Phyks/CitizenWatt-refactor/receiver/hardware/2017-02-15-201954.png

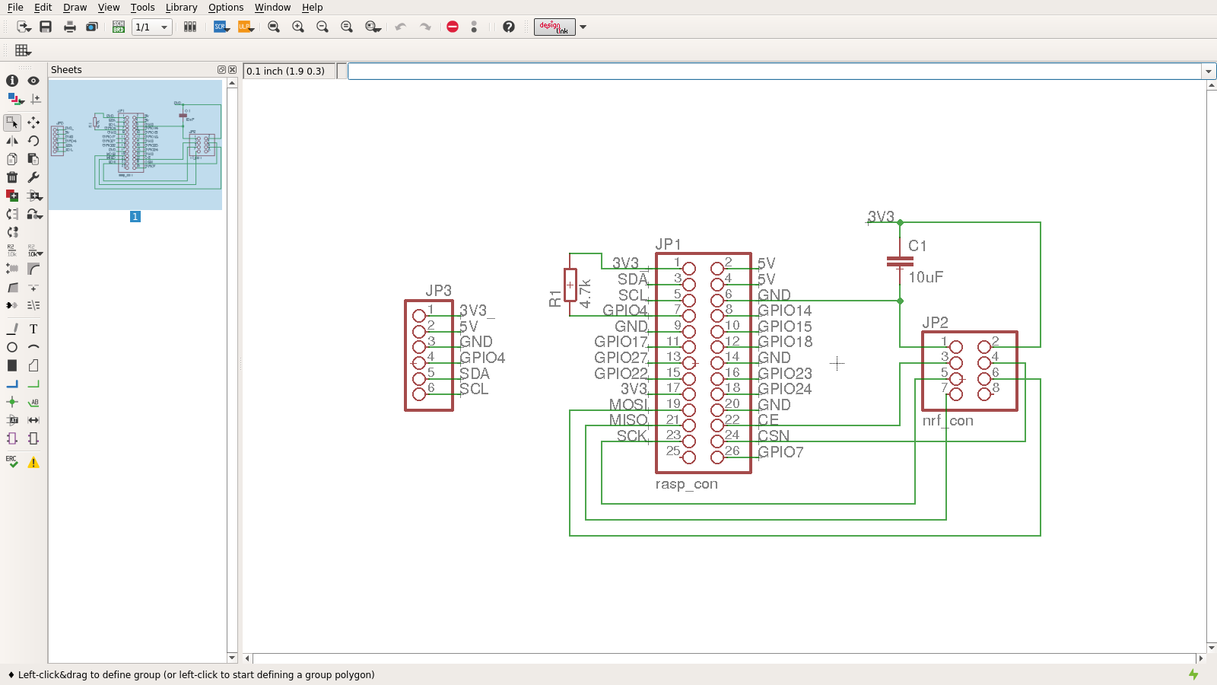
receiver/hardware/2017-02-15-201954.png
