Phyks/CitizenWatt-refactor/receiver/hardware/2017-02-15-202006.png

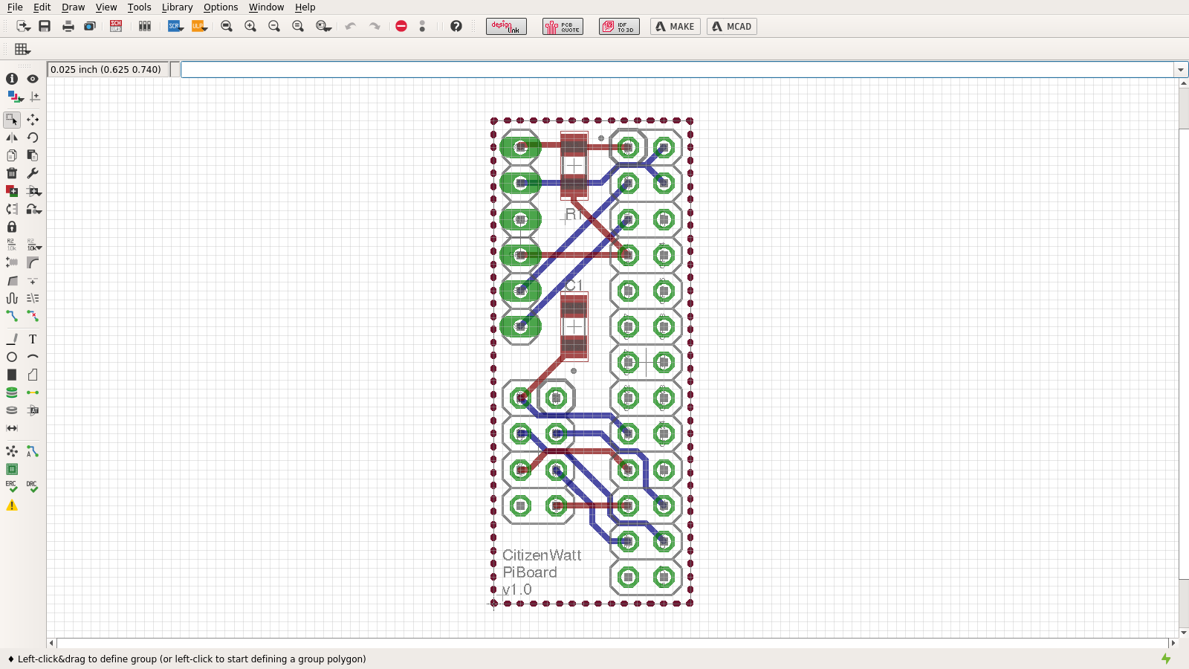
receiver/hardware/2017-02-15-202006.png
